LyubomirNachev/Dyskata_s_elektrichestvoto/Elektro_kontroler/Elektro_kontroler.kicad_pcb

## KiCad design Schematic/DACAndOutput.kicad_sch

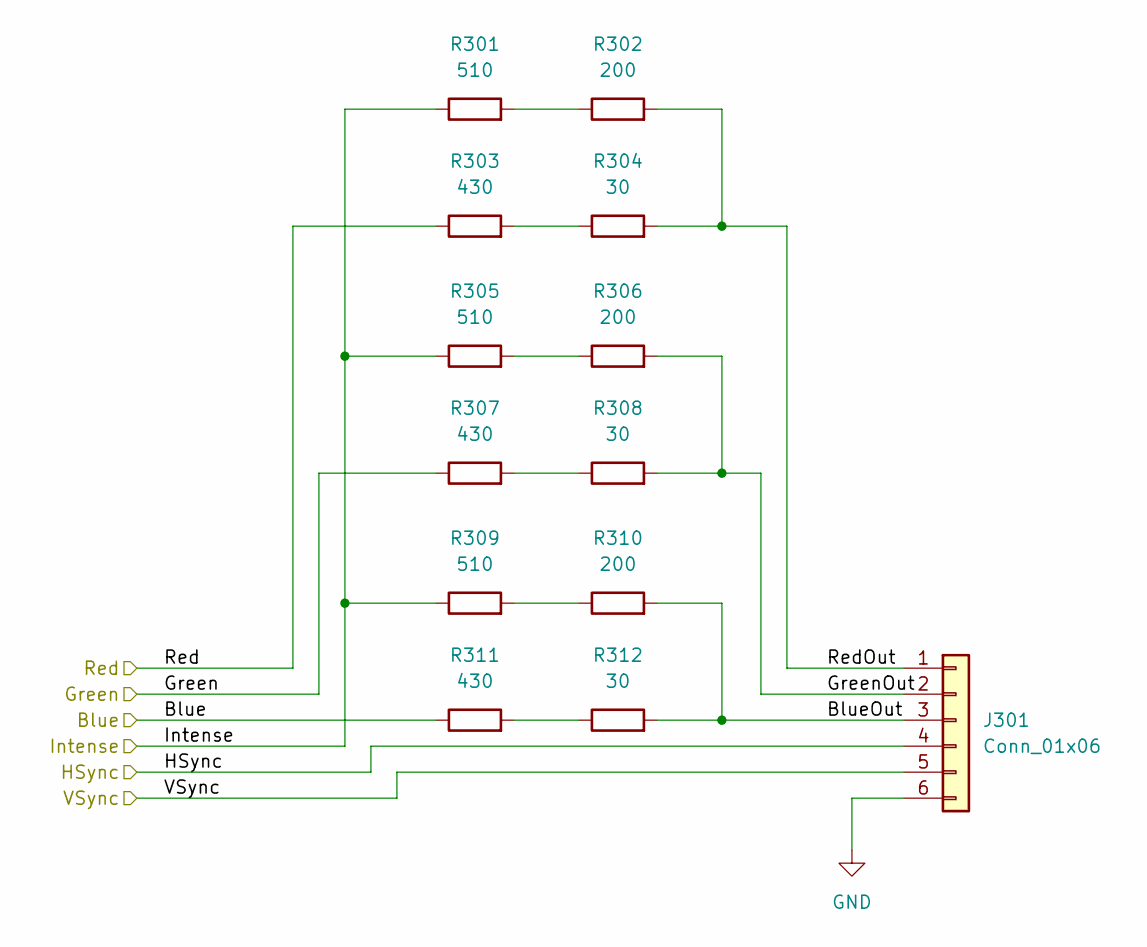
[picture p2: schematic DACAndOutput.kicad_sch]

Parts:
J301: Conn_01x06
R301, R305, R309: 510
R302, R306, R310: 200
R303, R307, R311: 430
R304, R308, R312: 30

Connections:
Blue: R311.1
BlueOut: J301.3, R310.2, R312.2
GND: J301.6
Green: R307.1
GreenOut: J301.2, R306.2, R308.2
HSync: J301.4
Intense: R301.1, R305.1, R309.1
unnamed: R301.2, R302.1
unnamed: R303.2, R304.1
unnamed: R305.2, R306.1
unnamed: R307.2, R308.1
unnamed: R309.2, R310.1
unnamed: R311.2, R312.1
Red: R303.1
RedOut: J301.1, R302.2, R304.2
VSync: J301.5
