LyubomirNachev/Dyskata_s_elektrichestvoto/Elektro_kontroler/Elektro_kontroler.kicad_pcb

## KiCad design Schematic/HostInterface.kicad_sch

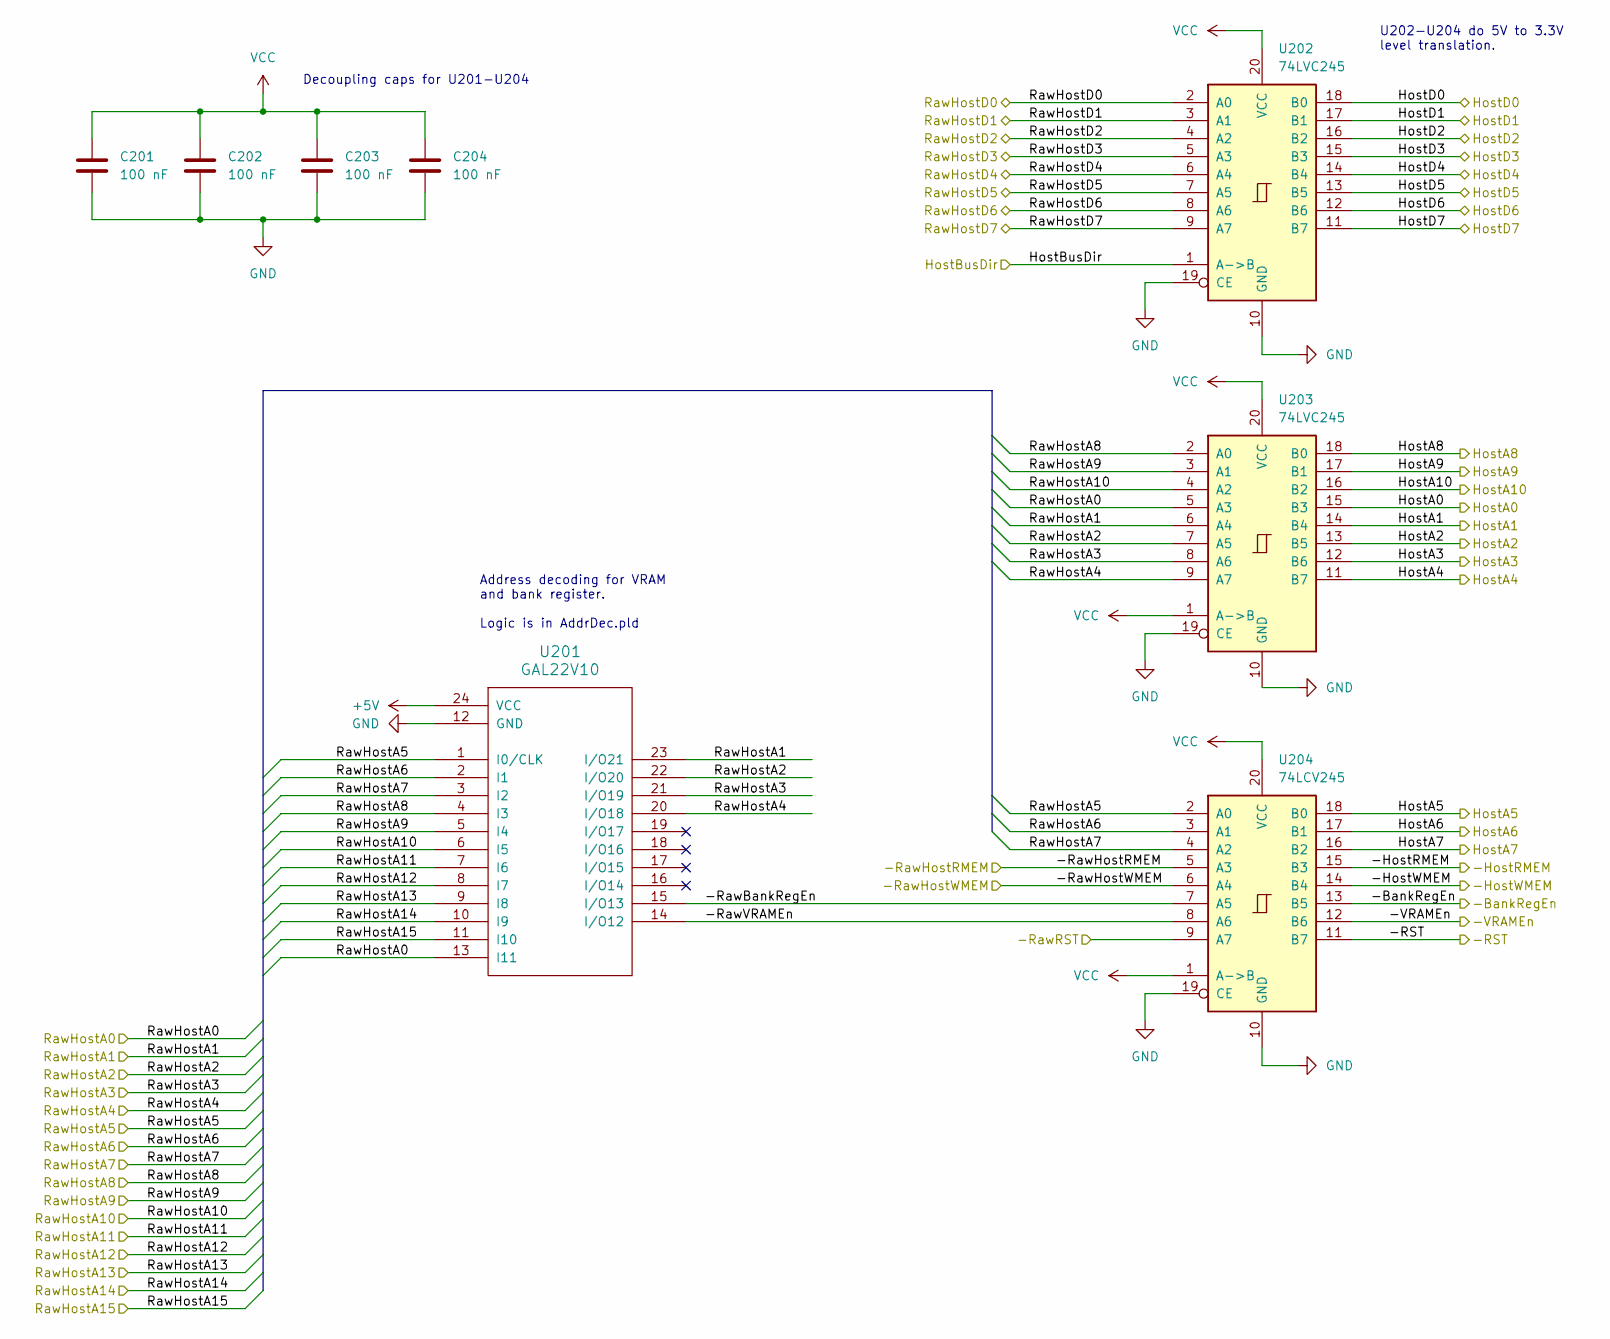
[picture p4: schematic HostInterface.kicad_sch]

Parts:
C201, C202, C203, C204: 100 nF
U201: GAL22V10
U202, U203: 74LVC245
U204: 74LCV245

Connections:
+5V: U201.24 (VCC)
-BankRegEn: U204.13 (B5)
-HostRMEM: U204.15 (B3)
-HostWMEM: U204.14 (B4)
-RST: U204.11 (B7)
-RawBankRegEn: U201.15 (I/O13), U204.7 (A5)
-RawHostRMEM: U204.5 (A3)
-RawHostWMEM: U204.6 (A4)
-RawRST: U204.9 (A7)
-RawVRAMEn: U201.14 (I/O12), U204.8 (A6)
-VRAMEn: U204.12 (B6)
GND: C201.2, C202.2, C203.2, C204.2, U201.12 (GND), U202.10 (GND), U202.19 (CE), U203.10 (GND), U203.19 (CE), U204.10 (GND), U204.19 (CE)
HostA0: U203.15 (B3)
HostA1: U203.14 (B4)
HostA2: U203.13 (B5)
HostA3: U203.12 (B6)
HostA4: U203.11 (B7)
HostA5: U204.18 (B0)
HostA6: U204.17 (B1)
HostA7: U204.16 (B2)
HostA8: U203.18 (B0)
HostA9: U203.17 (B1)
HostA10: U203.16 (B2)
HostBusDir: U202.1 (A->B)
HostD0: U202.18 (B0)
HostD1: U202.17 (B1)
HostD2: U202.16 (B2)
HostD3: U202.15 (B3)
HostD4: U202.14 (B4)
HostD5: U202.13 (B5)
HostD6: U202.12 (B6)
HostD7: U202.11 (B7)
RawHostA0: U201.13 (I11), U203.5 (A3)
RawHostA1: U201.23 (I/O21), U203.6 (A4)
RawHostA2: U201.22 (I/O20), U203.7 (A5)
RawHostA3: U201.21 (I/O19), U203.8 (A6)
RawHostA4: U201.20 (I/O18), U203.9 (A7)
RawHostA5: U201.1 (I0/CLK), U204.2 (A0)
RawHostA6: U201.2 (I1), U204.3 (A1)
RawHostA7: U201.3 (I2), U204.4 (A2)
RawHostA8: U201.4 (I3), U203.2 (A0)
RawHostA9: U201.5 (I4), U203.3 (A1)
RawHostA10: U201.6 (I5), U203.4 (A2)
RawHostA11: U201.7 (I6)
RawHostA12: U201.8 (I7)
RawHostA13: U201.9 (I8)
RawHostA14: U201.10 (I9)
RawHostA15: U201.11 (I10)
RawHostD0: U202.2 (A0)
RawHostD1: U202.3 (A1)
RawHostD2: U202.4 (A2)
RawHostD3: U202.5 (A3)
RawHostD4: U202.6 (A4)
RawHostD5: U202.7 (A5)
RawHostD6: U202.8 (A6)
RawHostD7: U202.9 (A7)
VCC: C201.1, C202.1, C203.1, C204.1, U202.20 (VCC), U203.1 (A->B), U203.20 (VCC), U204.1 (A->B), U204.20 (VCC)

Notes on the sheet:
Decoupling caps for U201-U204
Address decoding for VRAM and bank register. Logic is in AddrDec.pld
U202-U204 do 5V to 3.3V level translation.
